girishgetl/esp32-ntp-clock/Display_PCB.kicad_sch

## KiCad design Display_PCB.kicad_sch (2026-05-26)

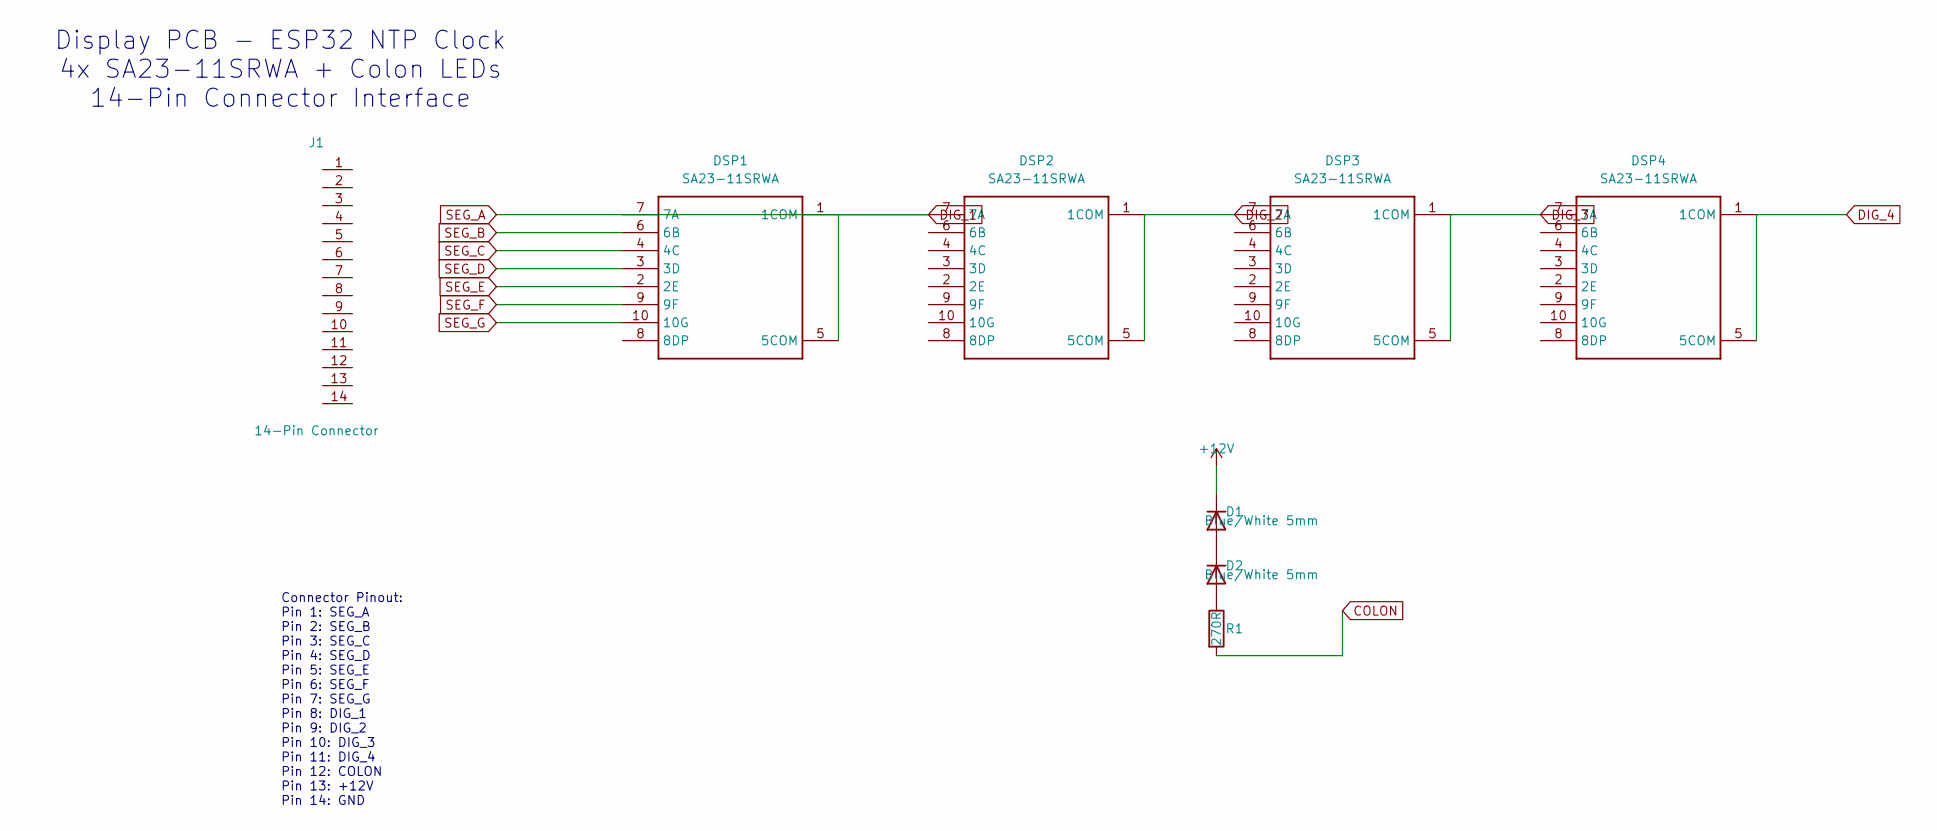
[picture p3: schematic Display_PCB.kicad_sch]

Parts:
D1, D2: Blue/White 5mm
DSP1, DSP2, DSP3, DSP4: SA23-11SRWA; 2.3_7-SEG_DIS
J1: 14-Pin Connector
R1: 270R

Connections:
+12V: D1.1 (K)
COLON: R1.2
DIG_1: DSP1.1 (1COM), DSP1.5 (5COM), DSP1.7 (7A), DSP2.7 (7A)
DIG_2: DSP2.1 (1COM), DSP2.5 (5COM), DSP3.7 (7A)
DIG_3: DSP3.1 (1COM), DSP3.5 (5COM), DSP4.7 (7A)
DIG_4: DSP4.1 (1COM), DSP4.5 (5COM)
unnamed: D1.2 (A), D2.1 (K)
unnamed: D2.2 (A), R1.1
SEG_B: DSP1.6 (6B)
SEG_C: DSP1.4 (4C)
SEG_D: DSP1.3 (3D)
SEG_E: DSP1.2 (2E)
SEG_F: DSP1.9 (9F)
SEG_G: DSP1.10 (10G)

Notes on the sheet:
Display PCB - ESP32 NTP Clock 4x SA23-11SRWA + Colon LEDs 14-Pin Connector Interface
Connector Pinout: Pin 1: SEG_A Pin 2: SEG_B Pin 3: SEG_C Pin 4: SEG_D Pin 5: SEG_E Pin 6: SEG_F Pin 7: SEG_G Pin 8: DIG_1 Pin 9: DIG_2 Pin 10: DIG_3 Pin 11: DIG_4 Pin 12: COLON Pin 13: +12V Pin 14: GND
