girishgetl/esp32-ntp-clock/ESP32_SUNW203CAW.kicad_sch

## KiCad design ESP32_SUNW203CAW.kicad_sch (2026-05-26)

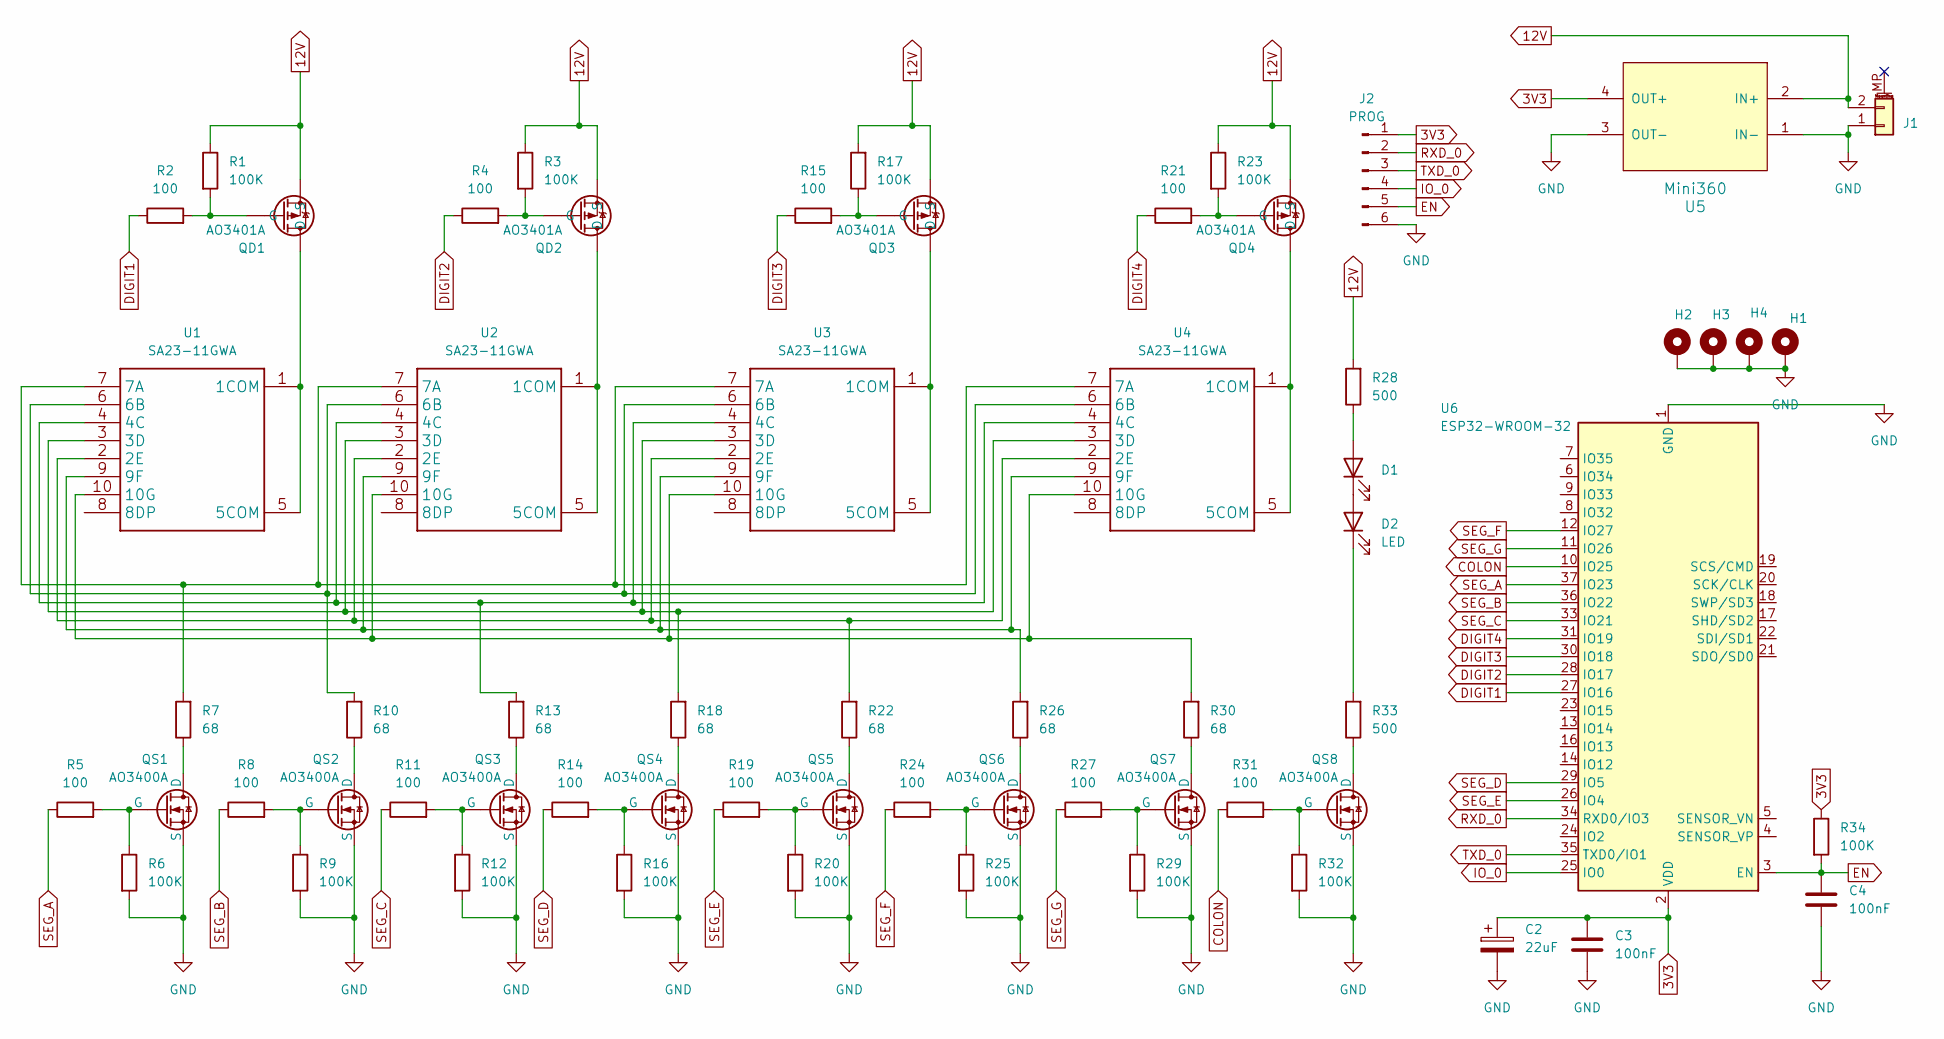
[picture p4: schematic ESP32_SUNW203CAW.kicad_sch]

Parts:
C2: 22uF; C_1206_3216Metric_Pad1.33x1.80mm_HandSolder
C3, C4: 100nF; C_1206_3216Metric_Pad1.33x1.80mm_HandSolder
D1, D2: LED; LED_D5.0mm_Clear
H1, H2, H3, H4: MountingHole_Pad; MountingHole_2.5mm_Pad_Via
J1: Conn_01x02_MountingPin; PinHeader_1x02_P2.54mm_Vertical
J2: PROG; PinHeader_1x06_P2.54mm_Vertical
QD1, QD2, QD3, QD4: AO3401A; SOT-23
QS1, QS2, QS3, QS4, QS5, QS6, QS7, QS8: AO3400A; SOT-23
R1, R3, R6, R9, R12, R16, R17, R20, R23, R25, R29, R32, R34: 100K; R_1206_3216Metric_Pad1.30x1.75mm_HandSolder
R2, R4, R5, R8, R11, R14, R15, R19, R21, R24, R27, R31: 100; R_1206_3216Metric_Pad1.30x1.75mm_HandSolder
R7, R10, R13, R18, R22, R26, R30: 68; R_1206_3216Metric_Pad1.30x1.75mm_HandSolder
R28, R33: 500; R_1206_3216Metric_Pad1.30x1.75mm_HandSolder
U1, U2, U3, U4: SA23-11GWA; SA23_2.3_7-SEG_DIS
U5: Mini360; Mini360-MP2307 Buck module
U6: ESP32-WROOM-32

Connections:
3V3: C2.1, C3.1, J2.1, R34.1, U5.4 (OUT+), U6.2 (VDD)
12V: J1.2, QD1.2 (S), QD2.2 (S), QD3.2 (S), QD4.2 (S), R1.1, R3.1, R17.2, R23.1, R28.2, U5.2 (IN+)
COLON: R31.1, U6.10 (IO25)
DIGIT1: R2.1, U6.27 (IO16)
DIGIT2: R4.1, U6.28 (IO17)
DIGIT3: R15.1, U6.30 (IO18)
DIGIT4: R21.1, U6.31 (IO19)
EN: C4.1, J2.5, R34.2, U6.3 (EN)
GND: C2.2, C3.2, C4.2, H1.1, H2.1, H3.1, H4.1, J1.1, J2.6, QS1.2 (S), QS2.2 (S), QS3.2 (S), QS4.2 (S), QS5.2 (S), QS6.2 (S), QS7.2 (S), QS8.2 (S), R6.2, R9.2, R12.2, R16.2, R20.2, R25.2, R29.2, R32.2, U5.1 (IN-), U5.3 (OUT-), U6.1 (GND), U6.15 (GND), U6.38 (GND), U6.39 (GND)
IO_0: J2.4, U6.25 (IO0)
unnamed: D1.1 (K), D2.2 (A)
unnamed: D1.2 (A), R28.1
unnamed: D2.1 (K), R33.2
unnamed: QD1.1 (G), R1.2, R2.2
unnamed: QD1.3 (D), U1.1 (1COM), U1.5 (5COM)
unnamed: QD2.1 (G), R3.2, R4.2
unnamed: QD2.3 (D), U2.1 (1COM), U2.5 (5COM)
unnamed: QD3.1 (G), R15.2, R17.1
unnamed: QD3.3 (D), U3.1 (1COM), U3.5 (5COM)
unnamed: QD4.1 (G), R21.2, R23.2
unnamed: QD4.3 (D), U4.1 (1COM), U4.5 (5COM)
unnamed: QS1.1 (G), R5.2, R6.1
unnamed: QS1.3 (D), R7.1
unnamed: QS2.1 (G), R8.2, R9.1
unnamed: QS2.3 (D), R10.1
unnamed: QS3.1 (G), R11.2, R12.1
unnamed: QS3.3 (D), R13.1
unnamed: QS4.1 (G), R14.2, R16.1
unnamed: QS4.3 (D), R18.1
unnamed: QS5.1 (G), R19.2, R20.1
unnamed: QS5.3 (D), R22.1
unnamed: QS6.1 (G), R24.2, R25.1
unnamed: QS6.3 (D), R26.1
unnamed: QS7.1 (G), R27.2, R29.1
unnamed: QS7.3 (D), R30.1
unnamed: QS8.1 (G), R31.2, R32.1
unnamed: QS8.3 (D), R33.1
unnamed: R7.2, U1.7 (7A), U2.7 (7A), U3.7 (7A), U4.7 (7A)
unnamed: R10.2, U1.6 (6B), U2.6 (6B), U3.6 (6B), U4.6 (6B)
unnamed: R13.2, U1.4 (4C), U2.4 (4C), U3.4 (4C), U4.4 (4C)
unnamed: R18.2, U1.3 (3D), U2.3 (3D), U3.3 (3D), U4.3 (3D)
unnamed: R22.2, U1.2 (2E), U2.2 (2E), U3.2 (2E), U4.2 (2E)
unnamed: R26.2, U1.9 (9F), U2.9 (9F), U3.9 (9F), U4.9 (9F)
unnamed: R30.2, U1.10 (10G), U2.10 (10G), U3.10 (10G), U4.10 (10G)
RXD_0: J2.2, U6.34 (RXD0/IO3)
SEG_A: R5.1, U6.37 (IO23)
SEG_B: R8.1, U6.36 (IO22)
SEG_C: R11.1, U6.33 (IO21)
SEG_D: R14.1, U6.29 (IO5)
SEG_E: R19.1, U6.26 (IO4)
SEG_F: R24.1, U6.12 (IO27)
SEG_G: R27.1, U6.11 (IO26)
TXD_0: J2.3, U6.35 (TXD0/IO1)
